rrowniak/ebike_ctrl/UI/firmware2/Core/Src/main.c

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
/* Includes ------------------------------------------------------------------*/
#include "main.h"

/* USER CODE BEGIN Includes */
#include "lcd/lcd_uc1611s_graphics.h"
#include "lcd/lcd_font_small.h"
#include "lcd/lcd_font_medium.h"
#include "lcd/lcd_font_large.h"
#include "screens.h"
#include <stdio.h>
/* USER CODE END Includes */


COM_InitTypeDef BspCOMInit;

ADC_HandleTypeDef hadc1;

FDCAN_HandleTypeDef hfdcan1;

I2C_HandleTypeDef hi2c1;

SPI_HandleTypeDef hspi1;

USART_HandleTypeDef husart1;

void SystemClock_Config(void);
static void MX_GPIO_Init(void);
static void MX_FDCAN1_Init(void);
static void MX_I2C1_Init(void);
static void MX_SPI1_Init(void);
static void MX_USART1_Init(void);
static void MX_ADC1_Init(void);

void welcome_screen();
static screens_data_t demo_data(void);
/**
  * @brief  The application entry point.
  * @retval int
  */
int main(void)
{

  /* MCU Configuration--------------------------------------------------------*/

  /* Reset of all peripherals, Initializes the Flash interface and the Systick. */
  HAL_Init();

  /* Configure the system clock */
  SystemClock_Config();

  /* Initialize all configured peripherals */
  MX_GPIO_Init();
  MX_FDCAN1_Init();
  MX_I2C1_Init();
  MX_SPI1_Init();
  MX_USART1_Init();
  MX_ADC1_Init();
  /* USER CODE BEGIN 2 */
  lcd_init();
  lcd_fill(0);
  welcome_screen();
  lcd_flush();
  HAL_Delay(1000);

  test_screen();
  lcd_flush();
  HAL_Delay(1000);
  /* USER CODE END 2 */

  /* Initialize leds */
  BSP_LED_Init(LED_GREEN);

  /* Initialize COM1 port (115200, 8 bits (7-bit data + 1 stop bit), no parity */
  BspCOMInit.BaudRate   = 115200;
  BspCOMInit.WordLength = COM_WORDLENGTH_8B;
  BspCOMInit.StopBits   = COM_STOPBITS_1;
  BspCOMInit.Parity     = COM_PARITY_NONE;
  BspCOMInit.HwFlowCtl  = COM_HWCONTROL_NONE;
  if (BSP_COM_Init(COM1, &BspCOMInit) != BSP_ERROR_NONE)
  {
    Error_Handler();
  }

  /* USER CODE BEGIN BSP */

  /* -- Sample board code to send message over COM1 port ---- */
  HAL_Delay(100);
  printf("Welcome to STM32 world !\n\r");

  /* -- Sample board code to switch on leds ---- */
  BSP_LED_On(LED_GREEN);

  /* USER CODE END BSP */

  /* Infinite loop */
  /* USER CODE BEGIN WHILE */
  while (1)
  {

/* -- Sample board code to toggle leds ---- */
       BSP_LED_Toggle(LED_GREEN);

       screens_data_t demo = demo_data();
       main_screen_p1(&demo);
       lcd_flush();
       HAL_Delay(250);

    /* USER CODE END WHILE */

    /* USER CODE BEGIN 3 */

  }
  /* USER CODE END 3 */
}

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
/* USER CODE BEGIN 4 */

/* Demo trip meters step through readings of 1, 2 and 3 digits, up and back
   down, so every text width the status bar has to fit is actually visible. */
#define TRIP_STEP_MS  1200u
#define DEMO_STEPS    5

static const uint32_t demo_dist_m[]  = { 0, 1200, 12000, 120000, 999900 };
static const uint32_t demo_wh_x10[]  = { 0, 1200, 12000, 120000,  99999 };
static const uint32_t demo_move_s[]  = { 0,   90,   600,   3600,  45296 };

/* Index into a demo table, walking to the end and back. */
static uint32_t demo_triangle(uint32_t tick, uint32_t step_ms)
{
  uint32_t i = (tick / step_ms) % (2 * (DEMO_STEPS - 1));
  return i < DEMO_STEPS ? i : 2 * (DEMO_STEPS - 1) - i;
}

static uint32_t s_rng_state;

static uint32_t rng_next(void)
{
  if (s_rng_state == 0)
    s_rng_state = HAL_GetTick();
  s_rng_state = s_rng_state * 1664525u + 1013904223u;
  return s_rng_state;
}

static int32_t clamp32(int32_t v, int32_t lo, int32_t hi)
{
  if (v < lo) return lo;
  if (v > hi) return hi;
  return v;
}

static screens_data_t demo_data(void)
{
  screens_data_t d;

  /* Speed wanders slowly instead of jumping every frame. */
  static int32_t speed_x10 = 220;
  speed_x10 = clamp32(speed_x10 + (int32_t)(rng_next() % 9) - 4, 0, 550);

  /* Trip meters step through 1, 2 and 3 digit readings; the clock runs at
     half the step rate so the two fields show different widths at times. */
  uint32_t tick = HAL_GetTick();
  uint32_t di = demo_triangle(tick, TRIP_STEP_MS);
  uint32_t ti = demo_triangle(tick + TRIP_STEP_MS, 2 * TRIP_STEP_MS);

  d.speed_x10   = speed_x10;
  d.watts       = speed_x10 / 2 + rng_next() % 60;
  d.temp_c      = 17 + rng_next() % 9;
  d.soc         = 70 + rng_next() % 16;
  d.voltage_x10 = 312 + rng_next() % 16;
  d.range_km    = 40 + rng_next() % 22;
  d.trip_m      = demo_dist_m[di];
  d.trip_wh_x10 = demo_wh_x10[di];
  d.trip_move_s = demo_move_s[ti];
  d.lights_on   = 1;
  d.fault       = 1;
  d.offline     = 1;
  d.alarm       = 1;
  d.page        = 1;
  d.pages       = 2;
  return d;
}

void welcome_screen() {
  lcd_text(10, 10, "ebike controller", font_large);
  lcd_text(10, 40, "by Rafal Rowniak", font_medium);
  lcd_text(10, 65, "v2.0 2026", font_small);
  lcd_text(10, 90, "hardware: STM32G431KB + UC1611S", font_small);
  lcd_text(10, 105, "screen:   240x128 COG LCD", font_small);
}

int _write(int file, char *ptr, int len)
{
  (void)file;
  HAL_UART_Transmit(&hcom_uart[COM1], (uint8_t *)ptr, (uint16_t)len, HAL_MAX_DELAY);
  return len;
}

/* USER CODE END 4 */

/* USER CODE BEGIN Header */
/**
  ******************************************************************************
  * @file           : main.c
  * @brief          : Main program body
  ******************************************************************************
  * @attention
  *
  * Copyright (c) 2026 STMicroelectronics.
  * All rights reserved.
  *
  * This software is licensed under terms that can be found in the LICENSE file
  * in the root directory of this software component.
  * If no LICENSE file comes with this software, it is provided AS-IS.
  *
  ******************************************************************************
  */
/* USER CODE END Header */

/**
  * @}
  */

/**
  * @}
  */

/**
  * @brief  This function is executed in case of error occurrence.
  * @retval None
  */
void Error_Handler(void)
{
  /* USER CODE BEGIN Error_Handler_Debug */
  /* User can add his own implementation to report the HAL error return state */
  __disable_irq();
  while (1)
  {
  }
  /* USER CODE END Error_Handler_Debug */
}
#ifdef USE_FULL_ASSERT
/**
  * @brief  Reports the name of the source file and the source line number
  *         where the assert_param error has occurred.
  * @param  file: pointer to the source file name
  * @param  line: assert_param error line source number
  * @retval None
  */
void assert_failed(uint8_t *file, uint32_t line)
{
  /* USER CODE BEGIN 6 */
  /* User can add his own implementation to report the file name and line number,
     ex: printf("Wrong parameters value: file %s on line %d\r\n", file, line) */
  /* USER CODE END 6 */
}
#endif /* USE_FULL_ASSERT */
