rrowniak/ebike_ctrl/UI/firmware2/Core/Src/lcd/lcd_font_large.c

#include "lcd/lcd_font_large.h"

static const uint8_t font_large_data[] = {
    /* 0x20 ' ' */
    0x00,0x00,0x00,0x00,0x00,0x00,0x00,0x00,0x00,0x00,0x00,0x00,
    0x00,0x00,0x00,0x00,0x00,0x00,0x00,0x00,0x00,0x00,0x00,0x00,
    0x00,0x00,0x00,0x00,0x00,0x00,0x00,0x00,0x00,0x00,0x00,0x00,
    /* 0x21 '!' */
    0x00,0x00,0x00,0x00,0x00,0x00,0xC0,0xC0,0xC0,0xC0,0xC0,0xC0,
    0xC0,0xC0,0xC0,0xC0,0xC0,0xC0,0xC0,0xC0,0xC0,0xC0,0xC0,0x00,
    0xC0,0xC0,0xC0,0xC0,0x00,0x00,0x00,0x00,0x00,0x00,0x00,0x00,
    /* 0x22 '"' */
    0x00,0x00,0xC0,0xC0,0xC0,0xC0,0xC0,0xC0,0xC0,0xC0,0x00,0x00,
    0x00,0x00,0x00,0x00,0x00,0x00,0x00,0x00,0x00,0x00,0x00,0x00,
    0x00,0x00,0x00,0x00,0x00,0x00,0x00,0x00,0x00,0x00,0x00,0x00,
    /* 0x23 '#' */
    0x00,0x00,0x00,0x00,0x00,0x00,0x30,0x30,0x30,0x30,0x30,0xFF,
    0xFF,0x30,0x30,0xFF,0xFF,0x30,0x30,0x30,0x30,0x30,0x00,0x00,
    0x00,0x00,0x00,0x00,0x00,0x00,0x00,0x00,0x00,0x00,0x00,0x00,
    /* 0x24 '$' */
    0x00,0x00,0x00,0x60,0x60,0xFC,0xFE,0xC6,0xC0,0xC0,0xC0,0xC0,
    0xFE,0xFE,0x06,0x06,0x06,0x06,0xC6,0xFE,0xFE,0x06,0x06,0x06,
    0x00,0x00,0x00,0x00,0x00,0x00,0x00,0x00,0x00,0x00,0x00,0x00,
    /* 0x25 '%' */
    0x00,0x00,0x00,0x00,0x00,0x00,0xC2,0xC6,0x0C,0x0C,0x18,0x18,
    0x30,0x30,0x60,0x60,0xC6,0x86,0x00,0x00,0x00,0x00,0x00,0x00,
    0x00,0x00,0x00,0x00,0x00,0x00,0x00,0x00,0x00,0x00,0x00,0x00,
    /* 0x26 '&' */
    0x00,0x00,0x00,0x00,0x00,0x00,0x70,0xD8,0xD8,0xD8,0xD8,0x70,
    0x70,0xF8,0xCC,0xCC,0xCC,0xCC,0xCC,0xCC,0x76,0x00,0x00,0x00,
    0x00,0x00,0x00,0x00,0x00,0x00,0x00,0x00,0x00,0x00,0x00,0x00,
    /* 0x27 ''' */
    0x00,0x00,0xC0,0xC0,0xC0,0xC0,0xC0,0xC0,0x00,0x00,0x00,0x00,
    0x00,0x00,0x00,0x00,0x00,0x00,0x00,0x00,0x00,0x00,0x00,0x00,
    0x00,0x00,0x00,0x00,0x00,0x00,0x00,0x00,0x00,0x00,0x00,0x00,
    /* 0x28 '(' */
    0x00,0x00,0x00,0x00,0x00,0x30,0x30,0x60,0x60,0xC0,0xC0,0xC0,
    0xC0,0xC0,0xC0,0xC0,0xC0,0xC0,0xC0,0xC0,0x60,0x60,0x30,0x30,
    0x00,0x00,0x00,0x00,0x00,0x00,0x00,0x00,0x00,0x00,0x00,0x00,
    /* 0x29 ')' */
    0x00,0x00,0x00,0x00,0x00,0xC0,0x60,0x60,0x30,0x30,0x30,0x30,
    0x30,0x30,0x30,0x30,0x30,0x30,0x30,0x30,0x60,0x60,0xC0,0xC0,
    0x00,0x00,0x00,0x00,0x00,0x00,0x00,0x00,0x00,0x00,0x00,0x00,
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
};

const lcd_font_t font_large = {
    .data         = font_large_data,
    .width        = 12,
    .height       = 36,
    .first_char   = 0x20,
    .last_char    = 0x7E,
    .bytes_per_char = 36,
    .row_major    = LCD_FONT_ROW_MAJOR,
};
