rrowniak/ebike_ctrl/UI/firmware2/Core/Src/lcd/lcd_font_medium.c

#include "lcd/lcd_font_medium.h"

static const uint8_t font_medium_data[] = {
    /* 0x20 ' ' */
    0x00,0x00,0x00,0x00,0x00,0x00,0x00,0x00,
    0x00,0x00,0x00,0x00,0x00,0x00,0x00,0x00,
    /* 0x21 '!' */
    0x00,0x00,0x00,0x18,0x3C,0x3C,0x3C,0x18,
    0x18,0x18,0x00,0x18,0x18,0x00,0x00,0x00,
    /* 0x22 '"' */
    0x00,0x00,0x66,0x66,0x66,0x24,0x00,0x00,
    0x00,0x00,0x00,0x00,0x00,0x00,0x00,0x00,
    /* 0x23 '#' */
    0x00,0x00,0x00,0x00,0x6C,0x6C,0xFE,0x6C,
    0x6C,0xFE,0x6C,0x6C,0x00,0x00,0x00,0x00,
    /* 0x24 '$' */
    0x00,0x00,0x18,0x18,0x7C,0xC6,0xC2,0xC0,
    0x7C,0x06,0x06,0x86,0xC6,0x7C,0x18,0x18,
    /* 0x25 '%' */
    0x00,0x00,0x00,0x00,0x00,0xC2,0xC6,0x0C,
    0x18,0x30,0x60,0xC6,0x86,0x00,0x00,0x00,
    /* 0x26 '&' */
    0x00,0x00,0x00,0x00,0x38,0x6C,0x6C,0x38,
    0x76,0xDC,0xCC,0xCC,0xCC,0x76,0x00,0x00,
    /* 0x27 ''' */
    0x00,0x00,0x30,0x30,0x30,0x60,0x00,0x00,
    0x00,0x00,0x00,0x00,0x00,0x00,0x00,0x00,
    /* 0x28 '(' */
    0x00,0x00,0x00,0x0C,0x18,0x30,0x30,0x30,
    0x30,0x30,0x30,0x18,0x0C,0x00,0x00,0x00,
    /* 0x29 ')' */
    0x00,0x00,0x00,0x30,0x18,0x0C,0x0C,0x0C,
    0x0C,0x0C,0x0C,0x18,0x30,0x00,0x00,0x00,
    /* 0x2A '*' */
    0x00,0x00,0x00,0x00,0x00,0x66,0x3C,0xFF,
    0x3C,0x66,0x00,0x00,0x00,0x00,0x00,0x00,
    /* 0x2B '+' */
    0x00,0x00,0x00,0x00,0x00,0x18,0x18,0x7E,
    0x18,0x18,0x00,0x00,0x00,0x00,0x00,0x00,
    /* 0x2C ',' */
    0x00,0x00,0x00,0x00,0x00,0x00,0x00,0x00,
    0x00,0x18,0x18,0x18,0x30,0x00,0x00,0x00,
    /* 0x2D '-' */
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
};

const lcd_font_t font_medium = {
    .data         = font_medium_data,
    .width        = 8,
    .height       = 16,
    .first_char   = 0x20,
    .last_char    = 0x7E,
    .bytes_per_char = 16,
    .row_major    = LCD_FONT_ROW_MAJOR,
};
