rrowniak/ebike_ctrl/Motherboard/firmware/tests/testmain.cpp

#define BOOST_TEST_MAIN
#define BOOST_TEST_DYN_LINK
#define BOOST_TEST_MODULE MOTHERBOARD_TESTS
// #include <boost/test/included/unit_test.hpp>
#include <boost/test/unit_test.hpp>

#include "TestLogic.hpp"
