rrowniak/ebike_ctrl/UI/firmware2/Core/Src/lcd/lcd_font_small.c

#include "lcd/lcd_font_small.h"

static const uint8_t font_small_data[] = {
    /* 0x20 ' ' */ 0x00, 0x00, 0x00, 0x00, 0x00, 0x00,
    /* 0x21 '!' */ 0x00, 0x00, 0x5F, 0x00, 0x00, 0x00,
    /* 0x22 '"' */ 0x00, 0x07, 0x00, 0x07, 0x00, 0x00,
    /* 0x23 '#' */ 0x14, 0x7F, 0x14, 0x7F, 0x14, 0x00,
    /* 0x24 '$' */ 0x24, 0x2A, 0x7F, 0x2A, 0x12, 0x00,
    /* 0x25 '%' */ 0x23, 0x13, 0x08, 0x64, 0x62, 0x00,
    /* 0x26 '&' */ 0x36, 0x49, 0x55, 0x22, 0x50, 0x00,
    /* 0x27 ''' */ 0x00, 0x05, 0x03, 0x00, 0x00, 0x00,
    /* 0x28 '(' */ 0x00, 0x1C, 0x22, 0x41, 0x00, 0x00,
    /* 0x29 ')' */ 0x00, 0x41, 0x22, 0x1C, 0x00, 0x00,
    /* 0x2A '*' */ 0x14, 0x08, 0x3E, 0x08, 0x14, 0x00,
    /* 0x2B '+' */ 0x08, 0x08, 0x3E, 0x08, 0x08, 0x00,
    /* 0x2C ',' */ 0x00, 0x50, 0x30, 0x00, 0x00, 0x00,
    /* 0x2D '-' */ 0x08, 0x08, 0x08, 0x08, 0x08, 0x00,
    /* 0x2E '.' */ 0x00, 0x60, 0x60, 0x00, 0x00, 0x00,
    /* 0x2F '/' */ 0x20, 0x10, 0x08, 0x04, 0x02, 0x00,
    /* 0x30 '0' */ 0x3E, 0x51, 0x49, 0x45, 0x3E, 0x00,
    /* 0x31 '1' */ 0x00, 0x42, 0x7F, 0x40, 0x00, 0x00,
    /* 0x32 '2' */ 0x42, 0x61, 0x51, 0x49, 0x46, 0x00,
    /* 0x33 '3' */ 0x21, 0x41, 0x45, 0x4B, 0x31, 0x00,
    /* 0x34 '4' */ 0x18, 0x14, 0x12, 0x7F, 0x10, 0x00,
    /* 0x35 '5' */ 0x27, 0x45, 0x45, 0x45, 0x39, 0x00,
    /* 0x36 '6' */ 0x3C, 0x4A, 0x49, 0x49, 0x30, 0x00,
    /* 0x37 '7' */ 0x01, 0x71, 0x09, 0x05, 0x03, 0x00,
    /* 0x38 '8' */ 0x36, 0x49, 0x49, 0x49, 0x36, 0x00,
    /* 0x39 '9' */ 0x06, 0x49, 0x49, 0x29, 0x1E, 0x00,
    /* 0x3A ':' */ 0x00, 0x36, 0x36, 0x00, 0x00, 0x00,
    /* 0x3B ';' */ 0x00, 0x56, 0x36, 0x00, 0x00, 0x00,
    /* 0x3C '<' */ 0x08, 0x14, 0x22, 0x41, 0x00, 0x00,
    /* 0x3D '=' */ 0x14, 0x14, 0x14, 0x14, 0x14, 0x00,
    /* 0x3E '>' */ 0x00, 0x41, 0x22, 0x14, 0x08, 0x00,
    /* 0x3F '?' */ 0x02, 0x01, 0x51, 0x09, 0x06, 0x00,
    /* 0x40 '@' */ 0x32, 0x49, 0x79, 0x41, 0x3E, 0x00,
    /* 0x41 'A' */ 0x7E, 0x11, 0x11, 0x11, 0x7E, 0x00,
    /* 0x42 'B' */ 0x7F, 0x49, 0x49, 0x49, 0x36, 0x00,
    /* 0x43 'C' */ 0x3E, 0x41, 0x41, 0x41, 0x22, 0x00,
    /* 0x44 'D' */ 0x7F, 0x41, 0x41, 0x22, 0x1C, 0x00,
    /* 0x45 'E' */ 0x7F, 0x49, 0x49, 0x49, 0x41, 0x00,
    /* 0x46 'F' */ 0x7F, 0x09, 0x09, 0x09, 0x01, 0x00,
    /* 0x47 'G' */ 0x3E, 0x41, 0x49, 0x49, 0x7A, 0x00,
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
};

const lcd_font_t font_small = {
    .data         = font_small_data,
    .width        = 6,
    .height       = 8,
    .first_char   = 0x20,
    .last_char    = 0x7E,
    .bytes_per_char = 6,
    .row_major    = LCD_FONT_COLUMN_MAJOR,
};
